xpix/XAmbi/Xambi-RPI-Gateway/IMG_2364.JPG

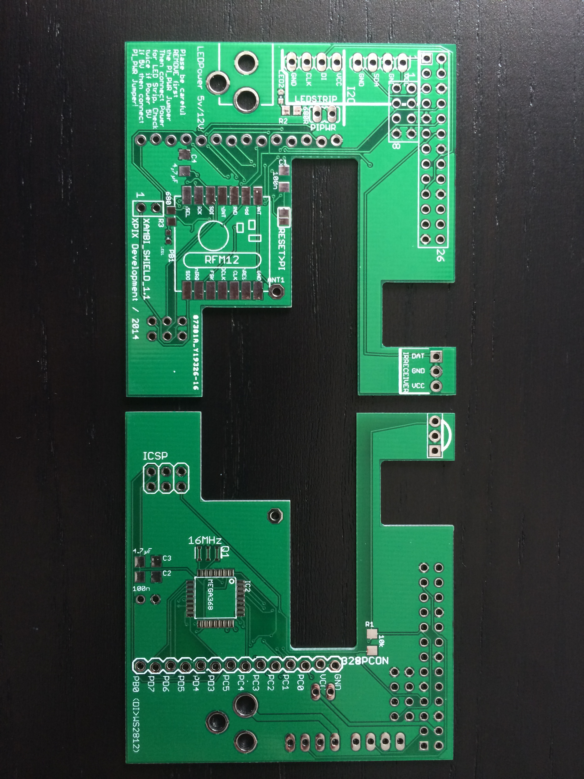
Xambi-RPI-Gateway/IMG_2364.JPG
