xpix/XAmbi/Xambi_kids/PROTOTYPE/xambikid_solar/IMG_2514.JPG

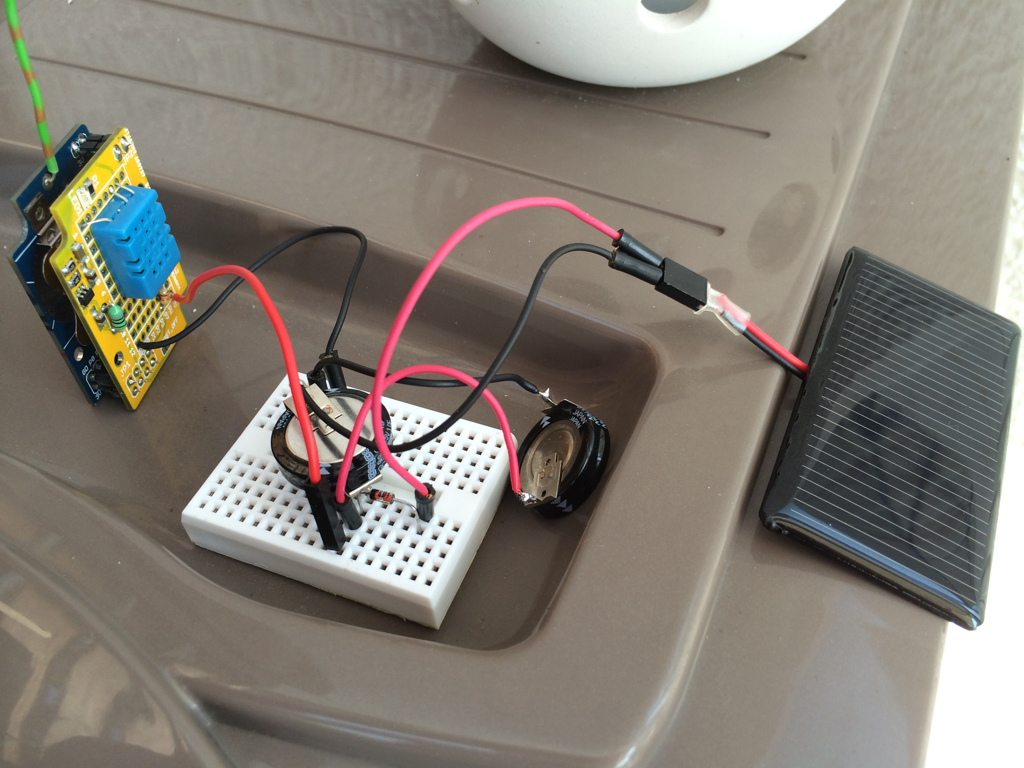
Xambi_kids/PROTOTYPE/xambikid_solar/IMG_2514.JPG
