xpix/XAmbi/Xambi_kids/PROTOTYPE/xambikid_solar/IMG_2515.JPG

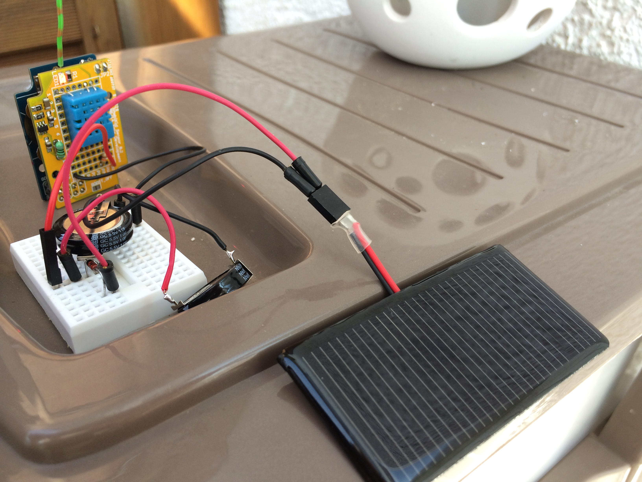
Xambi_kids/PROTOTYPE/xambikid_solar/IMG_2515.JPG
