xpix/XAmbi/Xambi_kids/xambikid_mailbox/IMG_2946.JPG

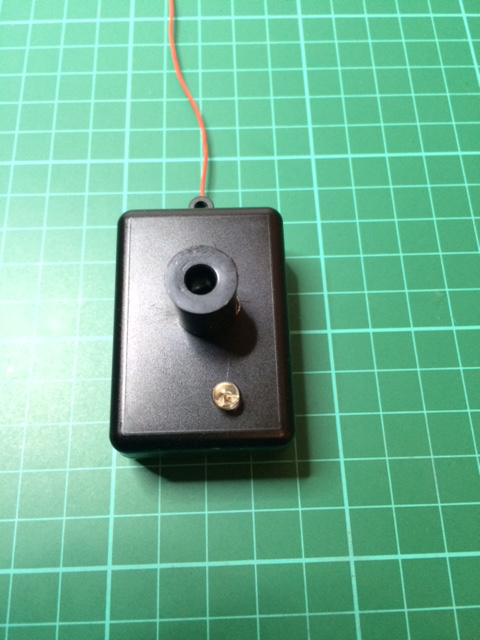
Xambi_kids/xambikid_mailbox/IMG_2946.JPG
