xpix/XAmbi/Xambi_kids/xambikid_mailbox/IMG_2948.JPG

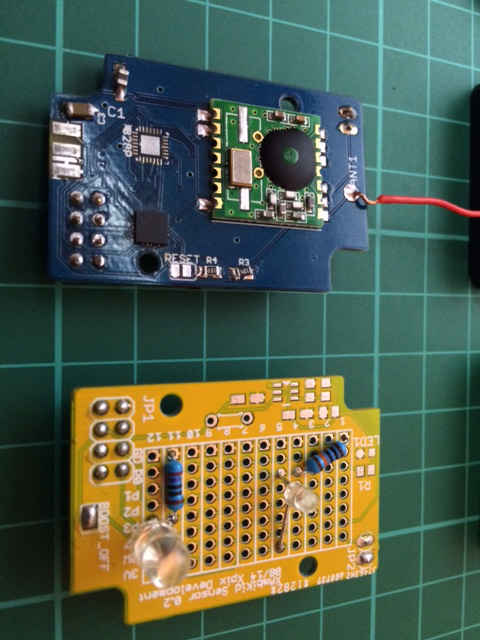
Xambi_kids/xambikid_mailbox/IMG_2948.JPG
