xpix/XAmbi/Xambi_kids/xambikid_sensorboard/xkid_sensor_0.1.brd

## EAGLE design Xambi_kids/xambikid_sensorboard/xkid_sensor_0.1.brd (2014-08-18)

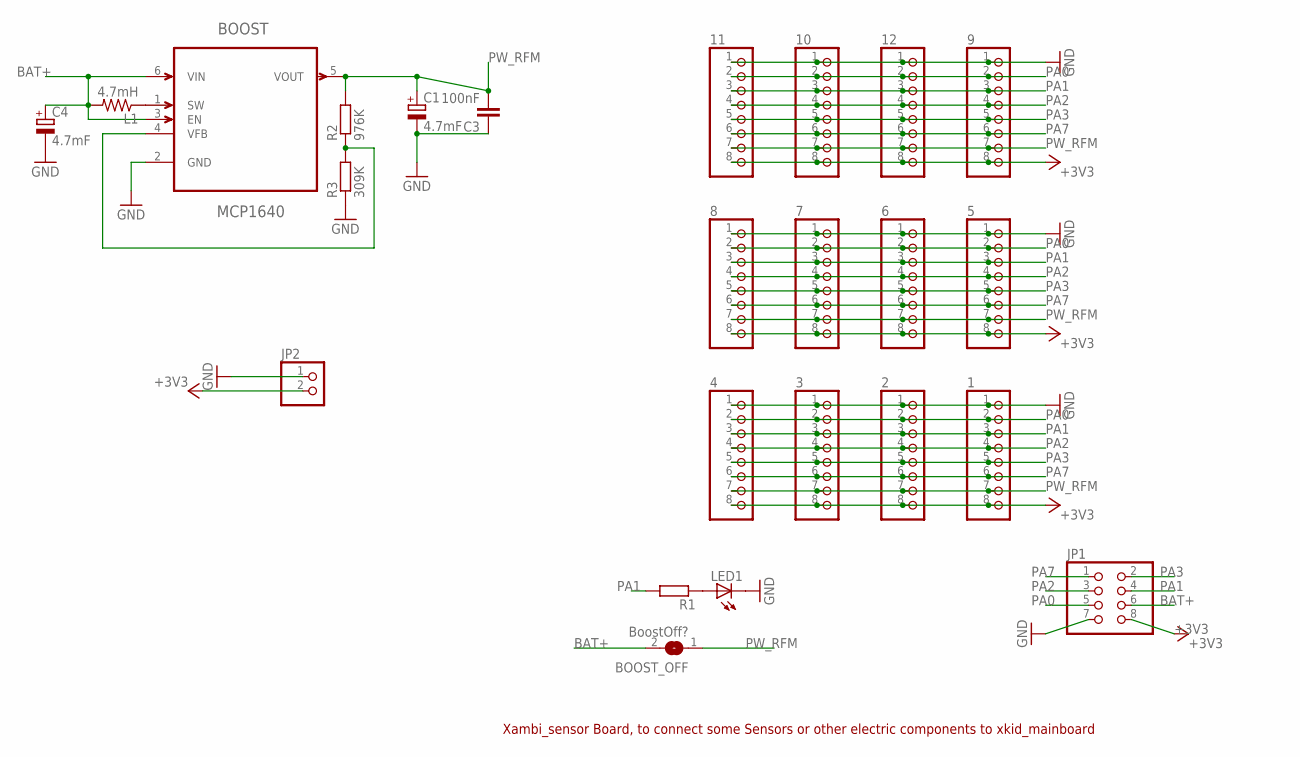
[picture p46: schematic xkid_sensor_0.1.sch]

Parts:
1, 2, 3, 4, 5, 6, 7, 8, 9, 10, 11, 12: PINHD-1X8_2.00; 1X08M
BOOST: MCP1640; SOT95P270X145-6N
BOOST_OFF: BoostOff?; SJ
C1, C4: 4.7mF; CT3216
C3: 100nF; C0805K
JP1: PINHD-2X4_2.54; 2X04
JP2: PINHD-1X2; 1X02
L1: 4.7mH; 0204/5
LED1: LEDCHIPLED_0805; CHIPLED_0805
R1: R-EU_R0805; R0805
R2: 976K; R0805
R3: 309K; R0805

Connections:
+3V3: 1.8, 2.8, 3.8, 4.8, 5.8, 6.8, 7.8, 8.8, 9.8, 10.8, 11.8, 12.8, JP1.8, JP2.2
BAT+: BOOST.3 (EN), BOOST.6 (VIN), BOOST_OFF.2, C4.+, JP1.6, L1.2
GND: 1.1, 2.1, 3.1, 4.1, 5.1, 6.1, 7.1, 8.1, 9.1, 10.1, 11.1, 12.1, BOOST.2 (GND), C1.-, C3.1, C4.-, JP1.7, JP2.1, LED1.C, R3.1
unnamed: LED1.A, R1.1
unnamed: BOOST.1 (SW), L1.1
unnamed: BOOST.4 (VFB), R2.1, R3.2
PA0: 1.2, 2.2, 3.2, 4.2, 5.2, 6.2, 7.2, 8.2, 9.2, 10.2, 11.2, 12.2, JP1.5
PA1: 1.3, 2.3, 3.3, 4.3, 5.3, 6.3, 7.3, 8.3, 9.3, 10.3, 11.3, 12.3, JP1.4, R1.2
PA2: 1.4, 2.4, 3.4, 4.4, 5.4, 6.4, 7.4, 8.4, 9.4, 10.4, 11.4, 12.4, JP1.3
PA3: 1.5, 2.5, 3.5, 4.5, 5.5, 6.5, 7.5, 8.5, 9.5, 10.5, 11.5, 12.5, JP1.2
PA7: 1.6, 2.6, 3.6, 4.6, 5.6, 6.6, 7.6, 8.6, 9.6, 10.6, 11.6, 12.6, JP1.1
PW_RFM: 1.7, 2.7, 3.7, 4.7, 5.7, 6.7, 7.7, 8.7, 9.7, 10.7, 11.7, 12.7, BOOST.5 (VOUT), BOOST_OFF.1, C1.+, C3.2, R2.2

Notes on the sheet:
Xambi_sensor Board, to connect some Sensors or other electric components to xkid_mainboard

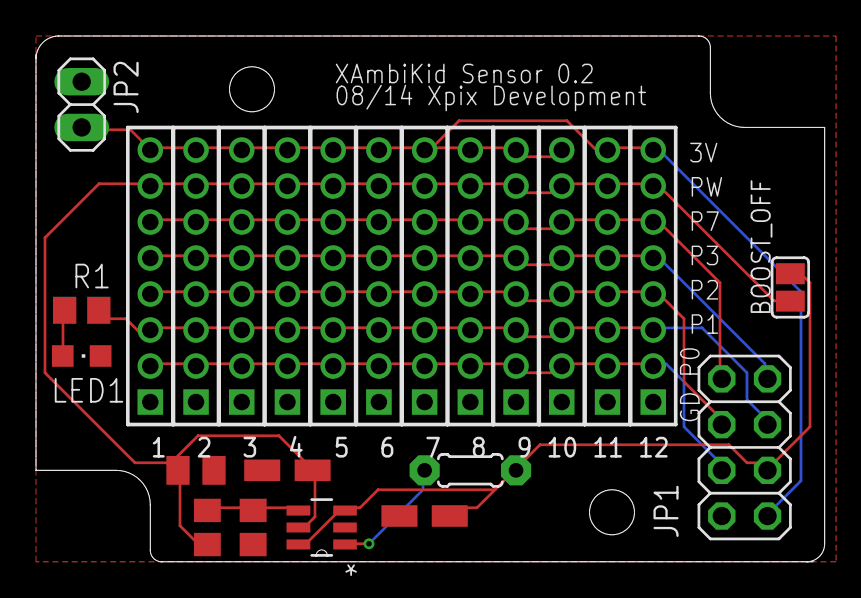
[picture p47: board xkid_sensor_0.1.brd from above]

Board: 2 copper layers, 43.8 x 29.2 mm, 24 parts (0 on the bottom side), 12 nets.
