xpix/XAmbi/Xambi_kids/xambikid_mainboard/IRSerial/ir_serial_tx/ir_serial_rx_ino/ir_serial_rx_ino.ino

//dirt cheap wireless RX
void setup()
{
 Serial.begin(1200);
 Serial.println('Init...');
 pinMode(13, OUTPUT);
}

void loop()
{
 // if incoming serial
 if (Serial.available()) {
   readSerial();
   digitalWrite(13, HIGH);
 } else {
   digitalWrite(13, LOW);
 }
 delay(10);
} 

void readSerial() {
 char val = Serial.read();
 Serial.print(val);
}
